RoseDaggerDev/MiniOscilloscope/Gloryshots/Size comparison.jpg

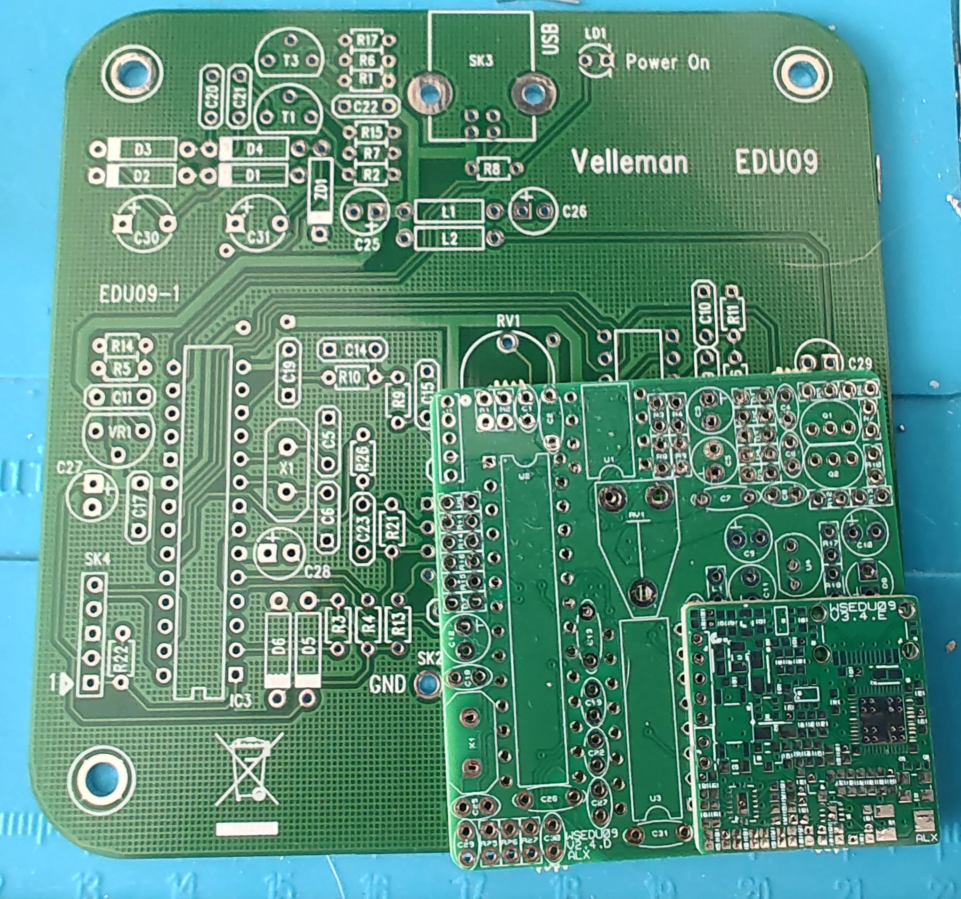
Gloryshots/Size comparison.jpg
