RoseDaggerDev/MiniOscilloscope/Gloryshots/SMD version front back.png

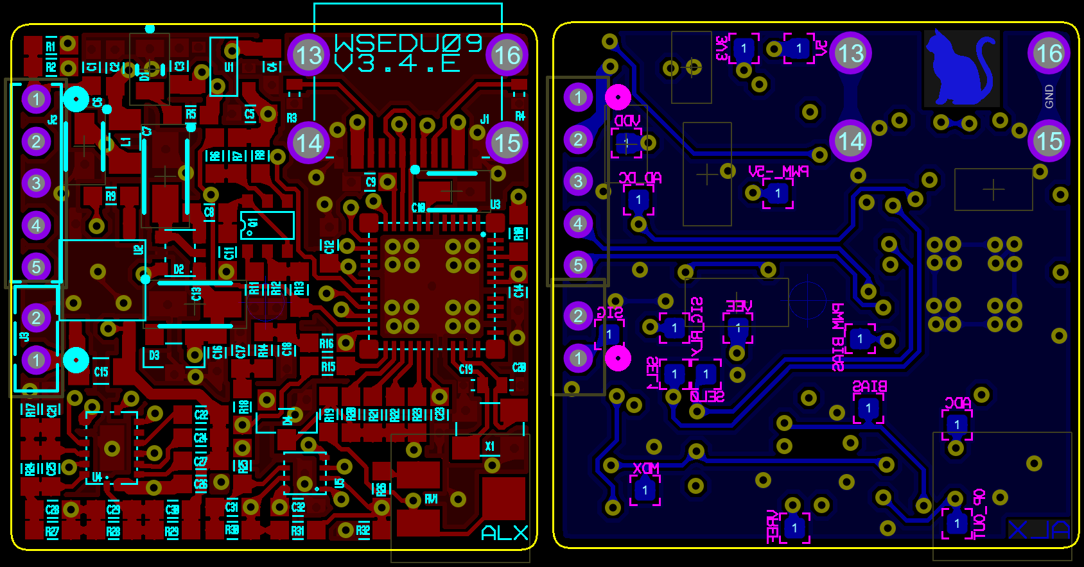
Gloryshots/SMD version front back.png
