RoseDaggerDev/MiniOscilloscope/Gloryshots/SMD version inner1 inner2.png

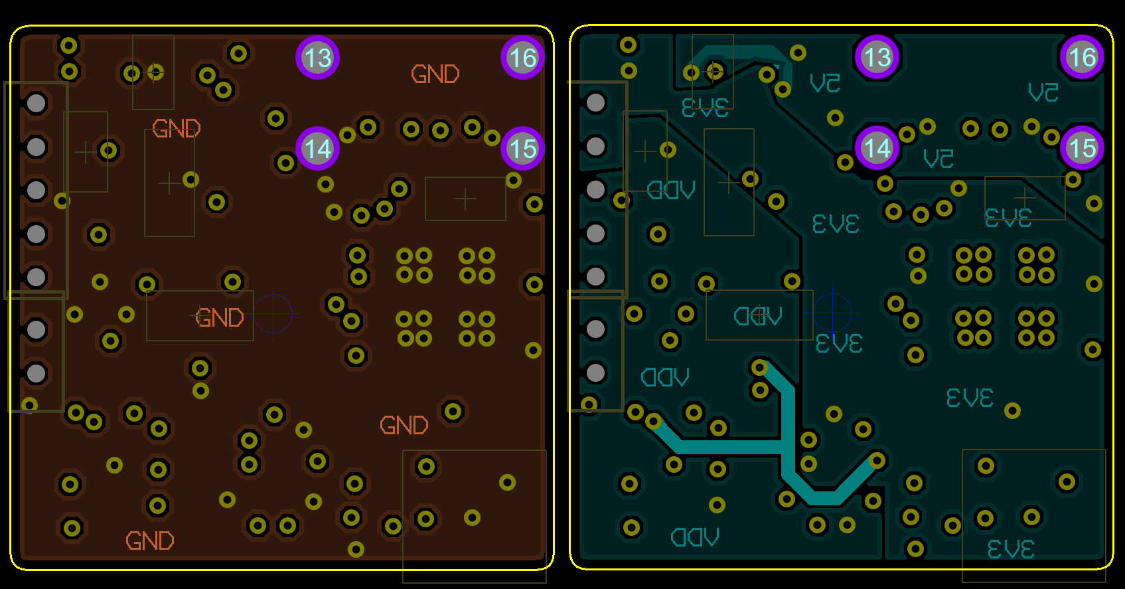
Gloryshots/SMD version inner1 inner2.png
